Somerset-Recon/bsides-badge-2024/software/03b_guerrilla_engagement.ino

#include <bitset>


void asciiArtGE(){
  SerialSAO.println(
"⠀⠀⠀⠀⠀⠀⠀⠀⠀⠀⠀⣠⠀⠀⠀⠀⠀⠀⠀⠀⠀⠀⠀⠀⠀⠀⠀⠀⠀⠀⠀⠀⠀⠀⠀⠀⠀⠀⠀⠀⠀⠀⠀⠀⠀⠀⠀⠀⠀⠀⠀⠀⠀⠀⠀\r\n"
"⠀⠀⠀⠀⠀⠀⠀⠀⠀⠀⠀⠓⠒⠀⠀⠀⠀⠀⠀⠀⠀⠀⠀⠀⢀⣀⣀⠀⠀⠀⠀⠀⢠⢤⣤⣤⡀⠀⠀⠀⠀⠀⠀⠀⠀⠀⠀⠀⠀⠀⠀⠀⠀⠀⠀\r\n"
"⠀⠀⠀⠀⠀⠀⠀⠀⠀⠀⠀⠀⠀⠀⠀⠀⠀⠀⠀⡠⠔⠒⠒⠲⠎⠀⠀⢹⡃⢀⣀⠀⠑⠃⠀⠈⢀⠔⠒⢢⠀⠀⠀⡖⠉⠉⠉⠒⢤⡀⠀⠀⠀⠀⠀\r\n"
"⠀⠀⠀⠀⠀⠀⠀⠀⠀⠀⢀⠔⠚⠙⠒⠒⠒⠤⡎⠀⠀⠀⠀⢀⣠⣴⣦⠀⠈⠘⣦⠑⠢⡀⠀⢰⠁⠀⠀⠀⠑⠰⠋⠁⠀⠀⠀⠀⠀⠈⢦⠀⠀⠀⠀\r\n"
"⠀⠀⠀⠀⠀⠀⠀⠀⠀⣸⠁⠀⠀⠀⠀⠀⠀⢰⠃⠀⣀⣀⡠⣞⣉⡀⡜⡟⣷⢟⠟⡀⣀⡸⠀⡎⠀⠀⠀⠀⠀⡇⠀⠀⠀⠀⠀⠀⠀⠀⣻⠀⠀⠀⠀\r\n"
"⢰⠂⠀⠀⠀⠀⠀⠀⠀⣗⠀⠀⢀⣀⣀⣀⣀⣀⣓⡞⢽⡚⣑⣛⡇⢸⣷⠓⢻⣟⡿⠻⣝⢢⠀⢇⣀⡀⠀⠀⠀⢈⠗⠒⢶⣶⣶⡾⠋⠉⠀⠀⠀⠀⠀\r\n"
"⠈⠉⠀⠀⠀⠀⠀⢀⠀⠈⠒⠊⠻⣷⣿⣚⡽⠃⠉⠀⠀⠙⠿⣌⠳⣼⡇⠀⣸⣟⡑⢄⠘⢸⢀⣾⠾⠥⣀⠤⠖⠁⠀⠀⠀⢸⡇⠀⠀⠀⠀⠀⢀⠀⠀\r\n"
"⠀⠀⠀⢰⢆⠀⢀⠏⡇⠀⡀⠀⠀⠀⣿⠉⠀⠀⠀⠀⠀⠀⠀⠈⢧⣸⡇⢐⡟⠀⠙⢎⢣⣿⣾⡷⠊⠉⠙⠢⠀⠀⠀⠀⠀⢸⡇⢀⠀⠀⠀⠀⠈⠣⡀\r\n"
"⠀⠀⠀⠘⡌⢣⣸⠀⣧⢺⢃⡤⢶⠆⣿⠀⠀⠀⠀⠀⠀⠀⠀⠀⠀⠙⣟⠋⢀⠔⣒⣚⡋⠉⣡⠔⠋⠉⢰⡤⣇⠀⠀⠀⠀⢸⡇⡇⠀⠀⠀⠀⠀⠀⠸\r\n"
"⠀⠀⠀⠀⠑⢄⢹⡆⠁⠛⣁⠔⠁⠀⣿⠀⠀⠀⠀⢸⡇⠀⠀⠀⠀⠀⣿⢠⡷⠋⠁⠀⠈⣿⡇⠀⠀⠀⠈⡇⠉⠀⠀⠀⠀⢸⡇⠀⠀⠀⠀⠀⠀⠀⠀\r\n"
"⠀⠀⠀⠀⠀⠀⠑⣦⡔⠋⠁⠀⠀⠀⣿⠀⠀⢠⡀⢰⣼⡇⠀⡀⠀⠀⣿⠀⠁⠀⠀⠀⠀⣿⣷⠀⠀⠀⠀⡇⠀⠀⢴⣤⠀⢸⡇⠀⠀⠀⠀⠀⠀⠀⠀\r\n"
"⠀⠀⠀⠀⠀⠀⢰⣿⡇⠀⠀⠀⠀⠀⣿⡀⠀⢨⣧⡿⠋⠀⠘⠛⠀⠀⣿⠀⠀⢀⠀⠀⠀⣿⣿⠀⠀⠀⠀⢲⠀⠀⠀⠀⠀⢸⡇⠀⠀⠀⠀⠀⠀⠀⠀\r\n"
"⠀⠀⠀⠀⠀⠀⢸⣿⡇⠀⠀⠀⠀⠀⢸⡧⡄⠀⠹⣇⡆⠀⠀⠀⠀⠀⣿⠀⢰⣏⠀⣿⣸⣿⣿⠀⠀⠀⠀⣼⠀⠀⠰⠗⠀⢸⡇⠀⠀⠀⠀⠀⠀⠀⠀\r\n"
"⠀⠀⠀⠀⠀⠀⢸⣿⡇⠀⠀⠀⠀⠀⢸⡇⣷⣛⣦⣿⢀⠈⠑⠀⢠⡆⣿⠐⢠⣟⠁⢸⠸⣿⣿⢱⣤⢀⠀⣼⠀⠀⢀⠀⠀⢸⡇⠀⠀⠀⠀⠀⠀⠀⠀\r\n"
"⠀⠀⠀⠀⠀⠀⢸⣿⡇⠀⢀⠀⠀⠀⢸⡇⠘⠫⣟⡇⠊⣣⠘⠛⣾⡆⢿⠀⠙⣿⢀⣘⡃⣿⣿⡏⠉⠒⠂⡿⠀⠰⣾⡄⠀⢸⡟⣽⣀⠀⠀⠀⠀⠀⠀\r\n"
"⠀⠀⠀⠀⠀⠀⠸⣿⡇⠀⠘⣾⠀⠀⢸⡇⢸⣇⡙⠣⠀⣹⣇⠀⠈⠧⢀⣀⣀⡏⣸⣿⣇⢹⣿⡇⢴⣴⣄⣀⡀⢰⣿⡇⠀⢸⣇⢿⡿⠀⠀⠀⠀⠀⠀\r\n"
"⠀⠀⠀⠀⠀⠀⠓⠁⠈⠻⢷⠾⠦⠤⠬⣅⣹⣿⣖⣶⣲⣈⡥⠤⠶⡖⠛⠒⠛⠁⠉⠛⠮⠐⢛⡓⠒⢛⠚⠒⠒⠒⠛⣚⣫⡼⠿⠿⣯⠛⠤⠀⠀⠀⠀\r\n"
"⠀⠀⠀⠀⠀⠀⠀⠀⠀⠀⠀⠀⠀⠉⠉⠉⠉⠉⠉⡉⠉⠁⠀⠀⠘⠓⠀⠀⠀⠀⠀⣀⣞⡿⡉⠉⠉⠉⠀⠀⠀⠀⠀⠀⠀⠀⠀⠀⠀⠀⠀⠀⠀⠀⠀\r\n"
"⠀⠀⠀⠀⠀⠀⠀⠀⠀⠀⠀⠀⠀⠀⠀⠀⠀⠀⠀⠹⣶⠏⠀⠀⠀⠀⠀⠀⠀⠀⠀⠀⠈⠉⠀⠀⠀⠀⠀⠀⠀⠀⠀⠀⠀⠀⠀⠀⠀⠀⠀⠀⠀⠀⠀\r\n\r\n\r\n"    
  );
}


void binaryPrint(String flag) { //prints string using two board leds (left=0, right=1)
  int zero = ATTACK_LED;
  int one = DEFEND_LED;
  int time_delay = 700;
  flag.trim();
  for (int i = 0; i <= sizeof(flag)/sizeof(flag[0]); i++) {
    std::bitset<8> binChar(flag.c_str()[i]);
    for (int bit = 7; bit >= 0; bit--) {
      if (binChar[bit] == 0) {
        digitalWrite(zero, 1);
        digitalWrite(one, 0);
      } else {
        digitalWrite(zero, 0);
        digitalWrite(one, 1);
      }
      delay(time_delay);
      digitalWrite(zero, 0);
      digitalWrite(one, 0);
      delay(time_delay / 2);
    }
  }
  return;
}

void GE() {
  clear();
  asciiArtGE();
  println("WELCOME TO GUERRILLA ENGAGEMENT.");
  println("ENEMY SCOUTS HAVE WIRETAPPED OUR COMMUNICATION LINES.");
  println("SWITCHING TO SECURE CHANNEL...");
  uint8_t flag[] = { 0xa4, 0x91, 0xdc, 0x4b, 0xe7, 0xdf, 0x18, 0x9b, 0xb1, 0x53, 0x47, 0x6b, 0x55, 0x02, 0x2c, 0x4b, 0xa1, 0x19, 0x06, 0xb9, 0x90, 0x92, 0xfa, 0xae, 0xe1, 0xab, 0x39, 0x0e, 0x99, 0xfb, 0xae, 0xe4 };
  binaryPrint(flagDecrypt(flag));
  return;
}
